AldanisVigo/QuestGamePIC32USBandC/src/config/default/definitions.h

/*******************************************************************************
  System Definitions

  File Name:
    definitions.h

  Summary:
    project system definitions.

  Description:
    This file contains the system-wide prototypes and definitions for a project.

 *******************************************************************************/

//DOM-IGNORE-BEGIN
/*******************************************************************************
* Copyright (C) 2025 Microchip Technology Inc. and its subsidiaries.
*
* Subject to your compliance with these terms, you may use Microchip software
* and any derivatives exclusively with Microchip products. It is your
* responsibility to comply with third party license terms applicable to your
* use of third party software (including open source software) that may
* accompany Microchip software.
*
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
* IN NO EVENT WILL MICROCHIP BE LIABLE FOR ANY INDIRECT, SPECIAL, PUNITIVE,
* INCIDENTAL OR CONSEQUENTIAL LOSS, DAMAGE, COST OR EXPENSE OF ANY KIND
* WHATSOEVER RELATED TO THE SOFTWARE, HOWEVER CAUSED, EVEN IF MICROCHIP HAS
* BEEN ADVISED OF THE POSSIBILITY OR THE DAMAGES ARE FORESEEABLE. TO THE
* FULLEST EXTENT ALLOWED BY LAW, MICROCHIP'S TOTAL LIABILITY ON ALL CLAIMS IN
* ANY WAY RELATED TO THIS SOFTWARE WILL NOT EXCEED THE AMOUNT OF FEES, IF ANY,
* THAT YOU HAVE PAID DIRECTLY TO MICROCHIP FOR THIS SOFTWARE.
 *******************************************************************************/
//DOM-IGNORE-END

#ifndef DEFINITIONS_H
#define DEFINITIONS_H

// *****************************************************************************
// *****************************************************************************
// Section: Included Files
// *****************************************************************************
// *****************************************************************************
#include <stdint.h>
#include <stddef.h>
#include <stdbool.h>
#include "usb/usb_device_cdc.h"
#include "usb/usb_cdc.h"
#include "peripheral/i2c/master/plib_i2c1_master.h"
#include "peripheral/clk/plib_clk.h"
#include "peripheral/gpio/plib_gpio.h"
#include "peripheral/evic/plib_evic.h"
#include "usb/usb_chapter_9.h"
#include "usb/usb_device.h"
#include "driver/usb/usbfs/drv_usbfs.h"
#include "system/int/sys_int.h"
#include "osal/osal.h"
#include "system/debug/sys_debug.h"
#include "app.h"



// DOM-IGNORE-BEGIN
#ifdef __cplusplus  // Provide C++ Compatibility

extern "C" {

#endif
// DOM-IGNORE-END

/* Device Information */
#define DEVICE_NAME          "PIC32MX270F256B"
#define DEVICE_ARCH          "MIPS"
#define DEVICE_FAMILY        "PIC32MX1168"
#define DEVICE_SERIES        "PIC32MX"

/* CPU clock frequency */
#define CPU_CLOCK_FREQUENCY 40000000U

// *****************************************************************************
// *****************************************************************************
// Section: System Functions
// *****************************************************************************
// *****************************************************************************

// *****************************************************************************
/* System Initialization Function

  Function:
    void SYS_Initialize( void *data )

  Summary:
    Function that initializes all modules in the system.

  Description:
    This function initializes all modules in the system, including any drivers,
    services, middleware, and applications.

  Precondition:
    None.

  Parameters:
    data            - Pointer to the data structure containing any data
                      necessary to initialize the module. This pointer may
                      be null if no data is required and default initialization
                      is to be used.

  Returns:
    None.

  Example:
    <code>
    SYS_Initialize ( NULL );

    while ( true )
    {
        SYS_Tasks ( );
    }
    </code>

  Remarks:
    This function will only be called once, after system reset.
*/

void SYS_Initialize( void *data );

// *****************************************************************************
/* System Tasks Function

Function:
    void SYS_Tasks ( void );

Summary:
    Function that performs all polled system tasks.

Description:
    This function performs all polled system tasks by calling the state machine
    "tasks" functions for all polled modules in the system, including drivers,
    services, middleware and applications.

Precondition:
    The SYS_Initialize function must have been called and completed.

Parameters:
    None.

Returns:
    None.

Example:
    <code>
    SYS_Initialize ( NULL );

    while ( true )
    {
        SYS_Tasks ( );
    }
    </code>

Remarks:
    If the module is interrupt driven, the system will call this routine from
    an interrupt context.
*/

void SYS_Tasks ( void );

// *****************************************************************************
// *****************************************************************************
// Section: Type Definitions
// *****************************************************************************
// *****************************************************************************

// *****************************************************************************
/* System Objects

Summary:
    Structure holding the system's object handles

Description:
    This structure contains the object handles for all objects in the
    MPLAB Harmony project's system configuration.

Remarks:
    These handles are returned from the "Initialize" functions for each module
    and must be passed into the "Tasks" function for each module.
*/

typedef struct
{
    SYS_MODULE_OBJ  usbDevObject0;

    SYS_MODULE_OBJ  drvUSBFSObject;


} SYSTEM_OBJECTS;

// *****************************************************************************
// *****************************************************************************
// Section: extern declarations
// *****************************************************************************
// *****************************************************************************

extern const USB_DEVICE_INIT usbDevInitData; 



extern SYSTEM_OBJECTS sysObj;

//DOM-IGNORE-BEGIN
#ifdef __cplusplus
}
#endif
//DOM-IGNORE-END

#endif /* DEFINITIONS_H */
/*******************************************************************************
 End of File
*/
