AldanisVigo/QuestGamePIC32USBandC/src/config/default/initialization.c

/*******************************************************************************
  System Initialization File

  File Name:
    initialization.c

  Summary:
    This file contains source code necessary to initialize the system.

  Description:
    This file contains source code necessary to initialize the system.  It
    implements the "SYS_Initialize" function, defines the configuration bits,
    and allocates any necessary global system resources,
 *******************************************************************************/

// DOM-IGNORE-BEGIN
/*******************************************************************************
* Copyright (C) 2025 Microchip Technology Inc. and its subsidiaries.
*
* Subject to your compliance with these terms, you may use Microchip software
* and any derivatives exclusively with Microchip products. It is your
* responsibility to comply with third party license terms applicable to your
* use of third party software (including open source software) that may
* accompany Microchip software.
*
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
* IN NO EVENT WILL MICROCHIP BE LIABLE FOR ANY INDIRECT, SPECIAL, PUNITIVE,
* INCIDENTAL OR CONSEQUENTIAL LOSS, DAMAGE, COST OR EXPENSE OF ANY KIND
* WHATSOEVER RELATED TO THE SOFTWARE, HOWEVER CAUSED, EVEN IF MICROCHIP HAS
* BEEN ADVISED OF THE POSSIBILITY OR THE DAMAGES ARE FORESEEABLE. TO THE
* FULLEST EXTENT ALLOWED BY LAW, MICROCHIP'S TOTAL LIABILITY ON ALL CLAIMS IN
* ANY WAY RELATED TO THIS SOFTWARE WILL NOT EXCEED THE AMOUNT OF FEES, IF ANY,
* THAT YOU HAVE PAID DIRECTLY TO MICROCHIP FOR THIS SOFTWARE.
 *******************************************************************************/
// DOM-IGNORE-END

// *****************************************************************************
// *****************************************************************************
// Section: Included Files
// *****************************************************************************
// *****************************************************************************
#include "configuration.h"
#include "definitions.h"
#include "device.h"


// ****************************************************************************
// ****************************************************************************
// Section: Configuration Bits
// ****************************************************************************
// ****************************************************************************

/*** DEVCFG0 ***/
#pragma config DEBUG =      OFF
#pragma config JTAGEN =     OFF
#pragma config ICESEL =     ICS_PGx1
#pragma config PWP =        OFF
#pragma config BWP =        OFF
#pragma config CP =         OFF


/*** DEVCFG1 ***/
#pragma config FNOSC =      PRIPLL
#pragma config FPBDIV =     DIV_1
#pragma config FSOSCEN =    OFF
#pragma config IESO =       OFF
#pragma config POSCMOD =    HS
#pragma config OSCIOFNC =   OFF
#pragma config FCKSM =      CSDCMD
#pragma config WDTPS =      PS1048576
#pragma config FWDTEN =     OFF
#pragma config WINDIS =     OFF
#pragma config FWDTWINSZ =  WINSZ_50


/*** DEVCFG2 ***/
#pragma config FPLLIDIV =   DIV_4
#pragma config FPLLMUL =    MUL_20
#pragma config FPLLODIV =   DIV_2
#pragma config UPLLEN =     ON
#pragma config UPLLIDIV =   DIV_4

/*** DEVCFG3 ***/
#pragma config FVBUSONIO =  OFF
#pragma config USERID =     0xffff
#pragma config PMDL1WAY =   ON
#pragma config IOL1WAY =    ON
#pragma config FUSBIDIO =   OFF





// *****************************************************************************
// *****************************************************************************
// Section: Driver Initialization Data
// *****************************************************************************
// *****************************************************************************
/* Following MISRA-C rules are deviated in the below code block */
/* MISRA C-2023 Rule 7.2 - Deviation record ID - H3_MISRAC_2023_R_7_2_DR_1 */
/* MISRA C-2023 Rule 11.1 - Deviation record ID - H3_MISRAC_2023_R_11_1_DR_1 */
/* MISRA C-2023 Rule 11.3 - Deviation record ID - H3_MISRAC_2023_R_11_3_DR_1 */
/* MISRA C-2023 Rule 11.8 - Deviation record ID - H3_MISRAC_2023_R_11_8_DR_1 */



// *****************************************************************************
// *****************************************************************************
// Section: System Data
// *****************************************************************************
// *****************************************************************************
/* Structure to hold the object handles for the modules in the system. */
SYSTEM_OBJECTS sysObj;

// *****************************************************************************
// *****************************************************************************
// Section: Library/Stack Initialization Data
// *****************************************************************************
// *****************************************************************************
/******************************************************
 * USB Driver Initialization
 ******************************************************/
 
static uint8_t __attribute__((aligned(512))) endPointTable1[DRV_USBFS_ENDPOINTS_NUMBER * 32];


static const DRV_USBFS_INIT drvUSBFSInit =
{
     /* Assign the endpoint table */
    .endpointTable= endPointTable1,

    /* Interrupt Source for USB module */
    .interruptSource = INT_SOURCE_USB,
    
    /* USB Controller to operate as USB Device */
    .operationMode = DRV_USBFS_OPMODE_DEVICE,
    
    .operationSpeed = USB_SPEED_FULL,
 
    /* Stop in idle */
    .stopInIdle = false,
    
    /* Suspend in sleep */
    .suspendInSleep = false,
 
    /* Identifies peripheral (PLIB-level) ID */
    .usbID = USB_ID_1,
    

};








// *****************************************************************************
// *****************************************************************************
// Section: System Initialization
// *****************************************************************************
// *****************************************************************************



// *****************************************************************************
// *****************************************************************************
// Section: Local initialization functions
// *****************************************************************************
// *****************************************************************************

/* MISRAC 2023 deviation block end */

/*******************************************************************************
  Function:
    void SYS_Initialize ( void *data )

  Summary:
    Initializes the board, services, drivers, application and other modules.

  Remarks:
 */

void SYS_Initialize ( void* data )
{

    /* MISRAC 2023 deviation block start */
    /* MISRA C-2023 Rule 2.2 deviated in this file.  Deviation record ID -  H3_MISRAC_2023_R_2_2_DR_1 */

    /* Start out with interrupts disabled before configuring any modules */
    (void)__builtin_disable_interrupts();

  
    CLK_Initialize();

    /* Configure KSEG0 as cacheable memory. This is needed for Prefetch Buffer */
    __builtin_mtc0(16, 0,(__builtin_mfc0(16, 0) | 0x3U));

    /* Set the SRAM wait states to One */
    BMXCONbits.BMXWSDRM = 1;




	GPIO_Initialize();

    I2C1_Initialize();

    /* MISRAC 2023 deviation block start */
    /* Following MISRA-C rules deviated in this block  */
    /* MISRA C-2023 Rule 11.3 - Deviation record ID - H3_MISRAC_2023_R_11_3_DR_1 */
    /* MISRA C-2023 Rule 11.8 - Deviation record ID - H3_MISRAC_2023_R_11_8_DR_1 */




    /* Initialize the USB device layer */
    sysObj.usbDevObject0 = USB_DEVICE_Initialize (USB_DEVICE_INDEX_0 , ( SYS_MODULE_INIT* ) & usbDevInitData);


    /* Initialize USB Driver */ 
    sysObj.drvUSBFSObject = DRV_USBFS_Initialize(DRV_USBFS_INDEX_0, (SYS_MODULE_INIT *) &drvUSBFSInit);    


    /* MISRAC 2023 deviation block end */
    APP_Initialize();


    EVIC_Initialize();

	/* Enable global interrupts */
    (void)__builtin_enable_interrupts();



    /* MISRAC 2023 deviation block end */
}

/*******************************************************************************
 End of File
*/
